Jef-frey/CalculatorKeypad/software/oled.cpp

#include <Arduino.h>
#include <SPI.h>
#include <U8g2lib.h>
#include <Wire.h>
#include "oled.h"

// SCL : 12
// SDA : 11
// RST : 10
// DC  : 9
// CS  : 46
// word count is 20 for the display using helvR18

#include <iostream>
using namespace std;

U8G2_SH1122_256X64_1_4W_HW_SPI u8g2(U8G2_R2, /* cs=*/ CS_PIN, /* dc=*/ DC_PIN, /* reset=*/ RST_PIN);

const uint8_t Helvetica_custom[2238] U8G2_FONT_SECTION("Helvetica_custom") = 
  "^\0\4\3\5\5\3\5\6\30\31\0\373\23\373\23\373\2\335\6\17\10\241!\12b\32\232\360\1E\224"
  "\1\42\13\306\264\243 \302\23\211\230\0#&+\32\272$\42%\42%\42$\42r\360 FDJD"
  "HDJD\346\340A\210*\21!\21)\21)\21!\0$)\313\326\265%)gt\20\62!\61!"
  "\242BD\205\210\324\204X\303\272\62\211)\21\32\21\32\221\22\211\211\3\231;I!\0%\61S\26\332"
  "-F&f\245HFLHFLHDNHD\320D\224F\36B\36D\206R\306PDHLF"
  "HLFHJH\225\224Y\34\11\0&&N\32\306Di\67\62&$&$&$'\42\311\322F"
  "d\211\242\11e$r\62b$C\23\42\7!\63t\0'\10\302\270\233p\60\21(\24\5{\241\243"
  "DFDF\211\214\376\221\214\42\31!\31\1)\26\5w\241 #$#$\243HF\377DF\211\214"
  "\210\214\14\0*\30\213\65\266\20\71'!%\243JBnpNBJF\225\204\334d\0+\16\214\65"
  "\272%\252\253\203\7S\242\272\2,\11\302\270\231`\21!\1-\10K\324\266\360A\0.\6b\30\232"
  "`/\20\214\65\272%*\217\366\340\301<ZQ)\0\60\33K\26\266Su\263DJDJb\252\216"
  "\357\252&\244D\244Dff\256j\0\61\14F\32\266\244\346\340 H\377\17\62\33K\26\266Cu\20"
  "#\64!&!G'\70(\70\67F\66\267\241\344\301\203\0\63\37K\26\266St\20#$\42&!"
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
  "FLBNB\220pT\245\250\244 \341\34\0z\23\312\25\262\360\300N\335\330\234\334\330\234\272\271\203"
  "\3\3{\17\6w\241$\243H\277Q$\245H\277R|\10\1{\231\360\301\0}\20\6w\241 \245"
  "H\277R$\243H\277Q\4~\15\212\270\272\61t\20Br\20\64\1\0\0\0\4\377\377\0";

void oled_initialize() {
  u8g2.begin();
}

void print_calculator(display_buf calculator_display) {
  u8g2.firstPage();
  do {
    u8g2.setFont(Helvetica_custom);
    u8g2.setCursor(256-u8g2.getStrWidth(calculator_display.top_display), 31);
    u8g2.println(calculator_display.top_display);
    u8g2.setCursor(256-u8g2.getStrWidth(calculator_display.bottom_display), 63);
    u8g2.println(calculator_display.bottom_display);
  } while ( u8g2.nextPage() );
}

void print_battery(battery battery_status) {
  u8g2.firstPage();
  do {
    u8g2.setFont(Helvetica_custom);
    u8g2.setCursor(0, 31);
    if (battery_status.pwr){
      u8g2.println("USB powered");
    } else {
      u8g2.println("Battery powered");
    }

    u8g2.setCursor(0, 63);
    u8g2.print("Battery: ");
    u8g2.print(battery_status.bat);
    u8g2.println("V");

  } while ( u8g2.nextPage() );
}
