Jef-frey/CalculatorKeypad/software/LinkedList.h

#ifndef LINKEDLIST_H
#define LINKEDLIST_H

#include <iostream>
using namespace std;

struct Node {
  long double operand;
  char        operator_type;
  Node *      next;
};

class LinkedList {
  Node *  head;
  Node *  tail;
  public:
    LinkedList();

    void enterNode(long double operand_in, char operator_in);

    void setOperator(char operator_in);

    long double computeFormula();

    void deleteHead();

    Node * deleteNode(Node * ptr);

    bool isEmpty();
};

#endif
